luqas11/battery-debugger/circuit/circuit.kicad_sch

## KiCad design circuit/circuit.kicad_sch (2026-07-12, an earlier design)

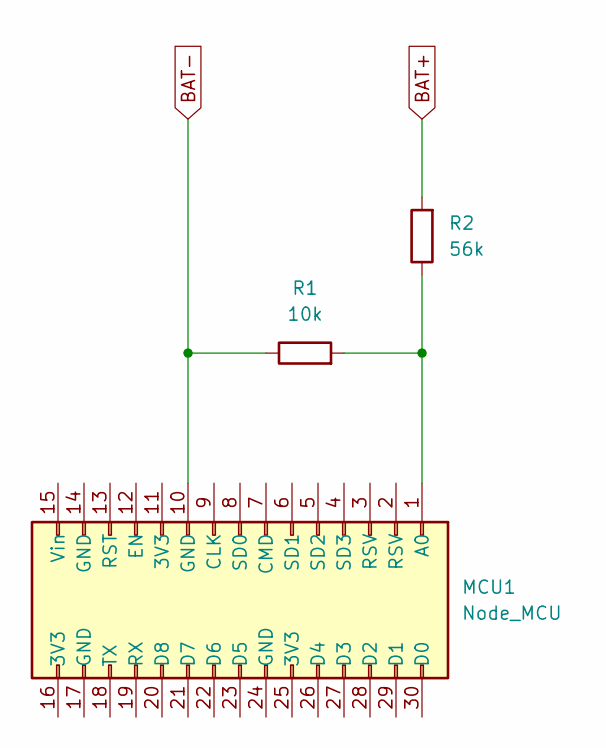
[picture p4: schematic circuit.kicad_sch]

Parts:
MCU1: Node_MCU
R1: 10k
R2: 56k

Connections:
BAT+: R2.2
BAT-: MCU1.10 (GND), R1.1
unnamed: MCU1.1 (A0), R1.2, R2.1
